gcc-robotics/prometheus/software/sistineChapel/commandProcessor.h

#include "robotArm.h"

#ifndef COMMAND_PROCESSOR
#define COMMAND_PROCESSOR

class CommandProcessor
{
	private:
		// Internal reference to the RobotArm
		RobotArm* arm;

	public:
		// Constructor
		CommandProcessor();

		void setup(RobotArm* robotArm);
		void armStatus();

		// -----------------------------------------------
		// Commands --------------------------------------
		// -----------------------------------------------

		// Command to set a joint to a specific angle
		void setJointAngle(String command);
		void getJointAngle(String command);
		void getJointLimits(String command);
		void getJointGains(String command);
		void setJointGains(String command);
		void getJointError(String command);

		void setClawState(String command);


		// Loop function for the CommandProcessor
		// Call in the Arduino loop function
		void loop();
};

#endif
